Franky55/A25_Business_Card_BestTeam/elec/BusinessCardV1/Components/TLC555CDR/TLC555CDR/TLC555CDR.step

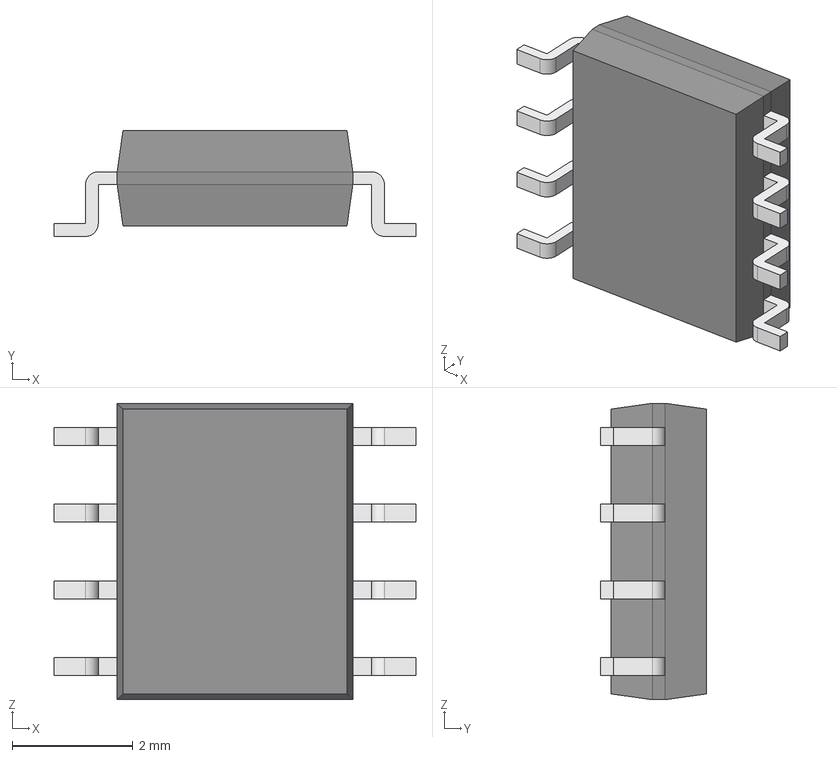
[picture p31: CAD file, 2025-11-23]
elec/BusinessCardV1/Components/TLC555CDR/TLC555CDR/TLC555CDR.step
5.99 x 1.75 x 4.91 mm
Body001 (Mirror #1) x 4
XY-plane x 12
X-axis x 12
