Franky55/A25_Business_Card_BestTeam/elec/BusinessCardV1/Components/TLV8544DR/D0014A.stp

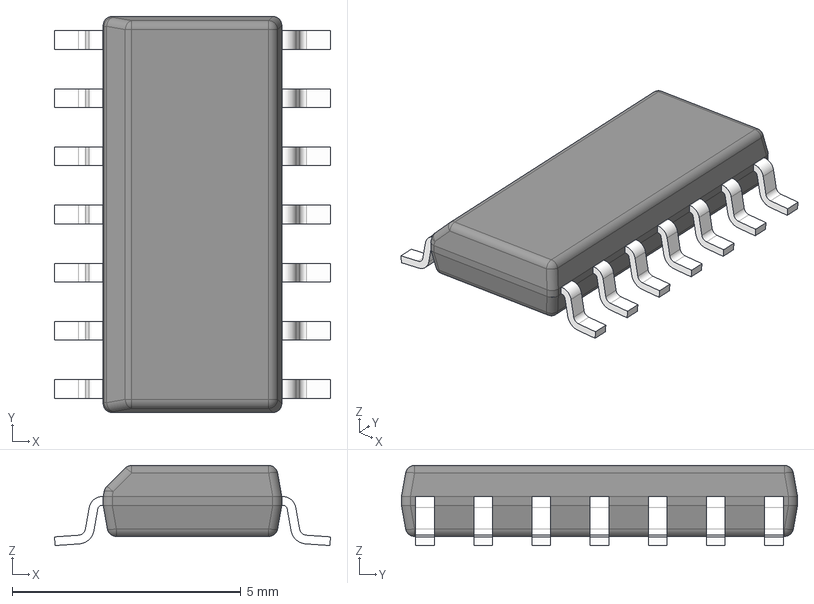
[picture p32: CAD file, 2025-10-28]
elec/BusinessCardV1/Components/TLV8544DR/D0014A.stp
6.03 x 8.65 x 1.75 mm
BODY-SO
LEAD-SO x 14
PIN1-ID
