Franky55/A25_Business_Card_BestTeam/elec/BusinessCardV1/Components/MCP73831T-2DCI_OT/MCP73831T-2DCI_OT.step

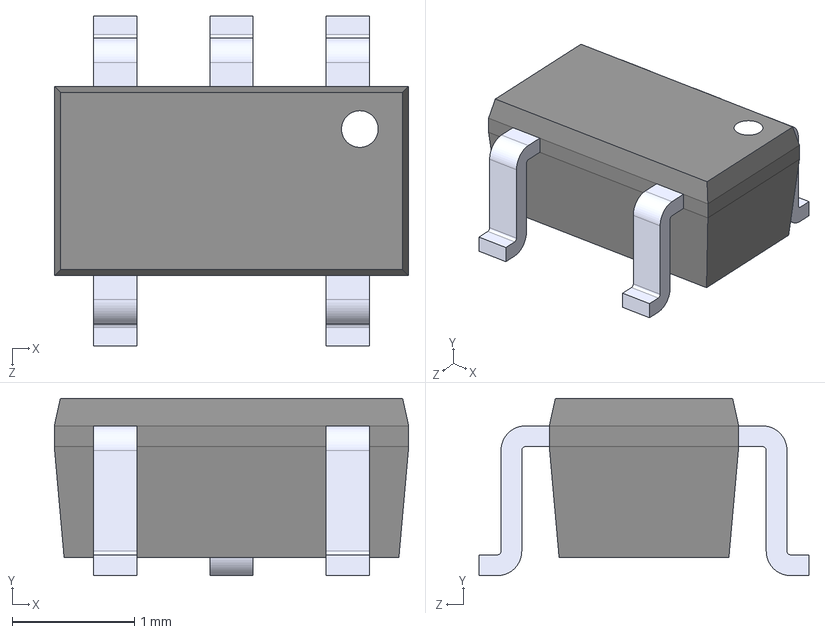
[picture p33: CAD file, 2025-10-28]
elec/BusinessCardV1/Components/MCP73831T-2DCI_OT/MCP73831T-2DCI_OT.step
2.90 x 1.45 x 2.70 mm
